Darksplat/Cellforge-4-Way-18650-Charger/Firmware/ASCD_Nano_PIO/ASCD_Nano_Cellforge/src/Secrets.h

#pragma once

// =====================================================
// Secrets / Configuration
// =====================================================

// WiFi (future use)
#define WIFI_SSID     ""
#define WIFI_PASSWORD ""

// API / Server (future use)
#define API_BASE_URL  ""
#define API_KEY       ""

// Feature flags
#define ENABLE_WIFI   0
#define ENABLE_API    0
